kocer/direct-sampling-sdr/ardc/sema/dogrudan_sdr_D.pdf

File: 03_bias.kicad_sch Surucu katlari File: 01_driver.kicad_sch

Final kat File: 02_final.kicad_sch Guc ve koruma

File: 04_detect.kicad_sch Cikis filtreleri File: 05_lpf.kicad_sch Bias servosu

Donanim CERN-OHL-S-2.0 | HDL ve yazilim GPL-3.0-only | belgeler CC-BY-SA-4.0
Copyright (c) 2026 TA4DTA - lisans CERN-OHL-S-2.0
Baglantilar PA_TASARIM.md sartnamesinden
Lisans: CERN-OHL-S v2 (donanim) · GPL-3.0 (HDL) · CC-BY-SA 4.0 (dok)
TEVITOL amator telsiz kulubu / TA4DTA
Sheet: /
File: dogrudan_sdr_D.kicad_sch
Title: dogrudan_sdr_D — dogrudan orneklemeli HF/VHF/UHF transceiver

Size: A3 | Rev: A
KiCad E.D.A. 10.0.5 | Id: 1/7 | F Date:

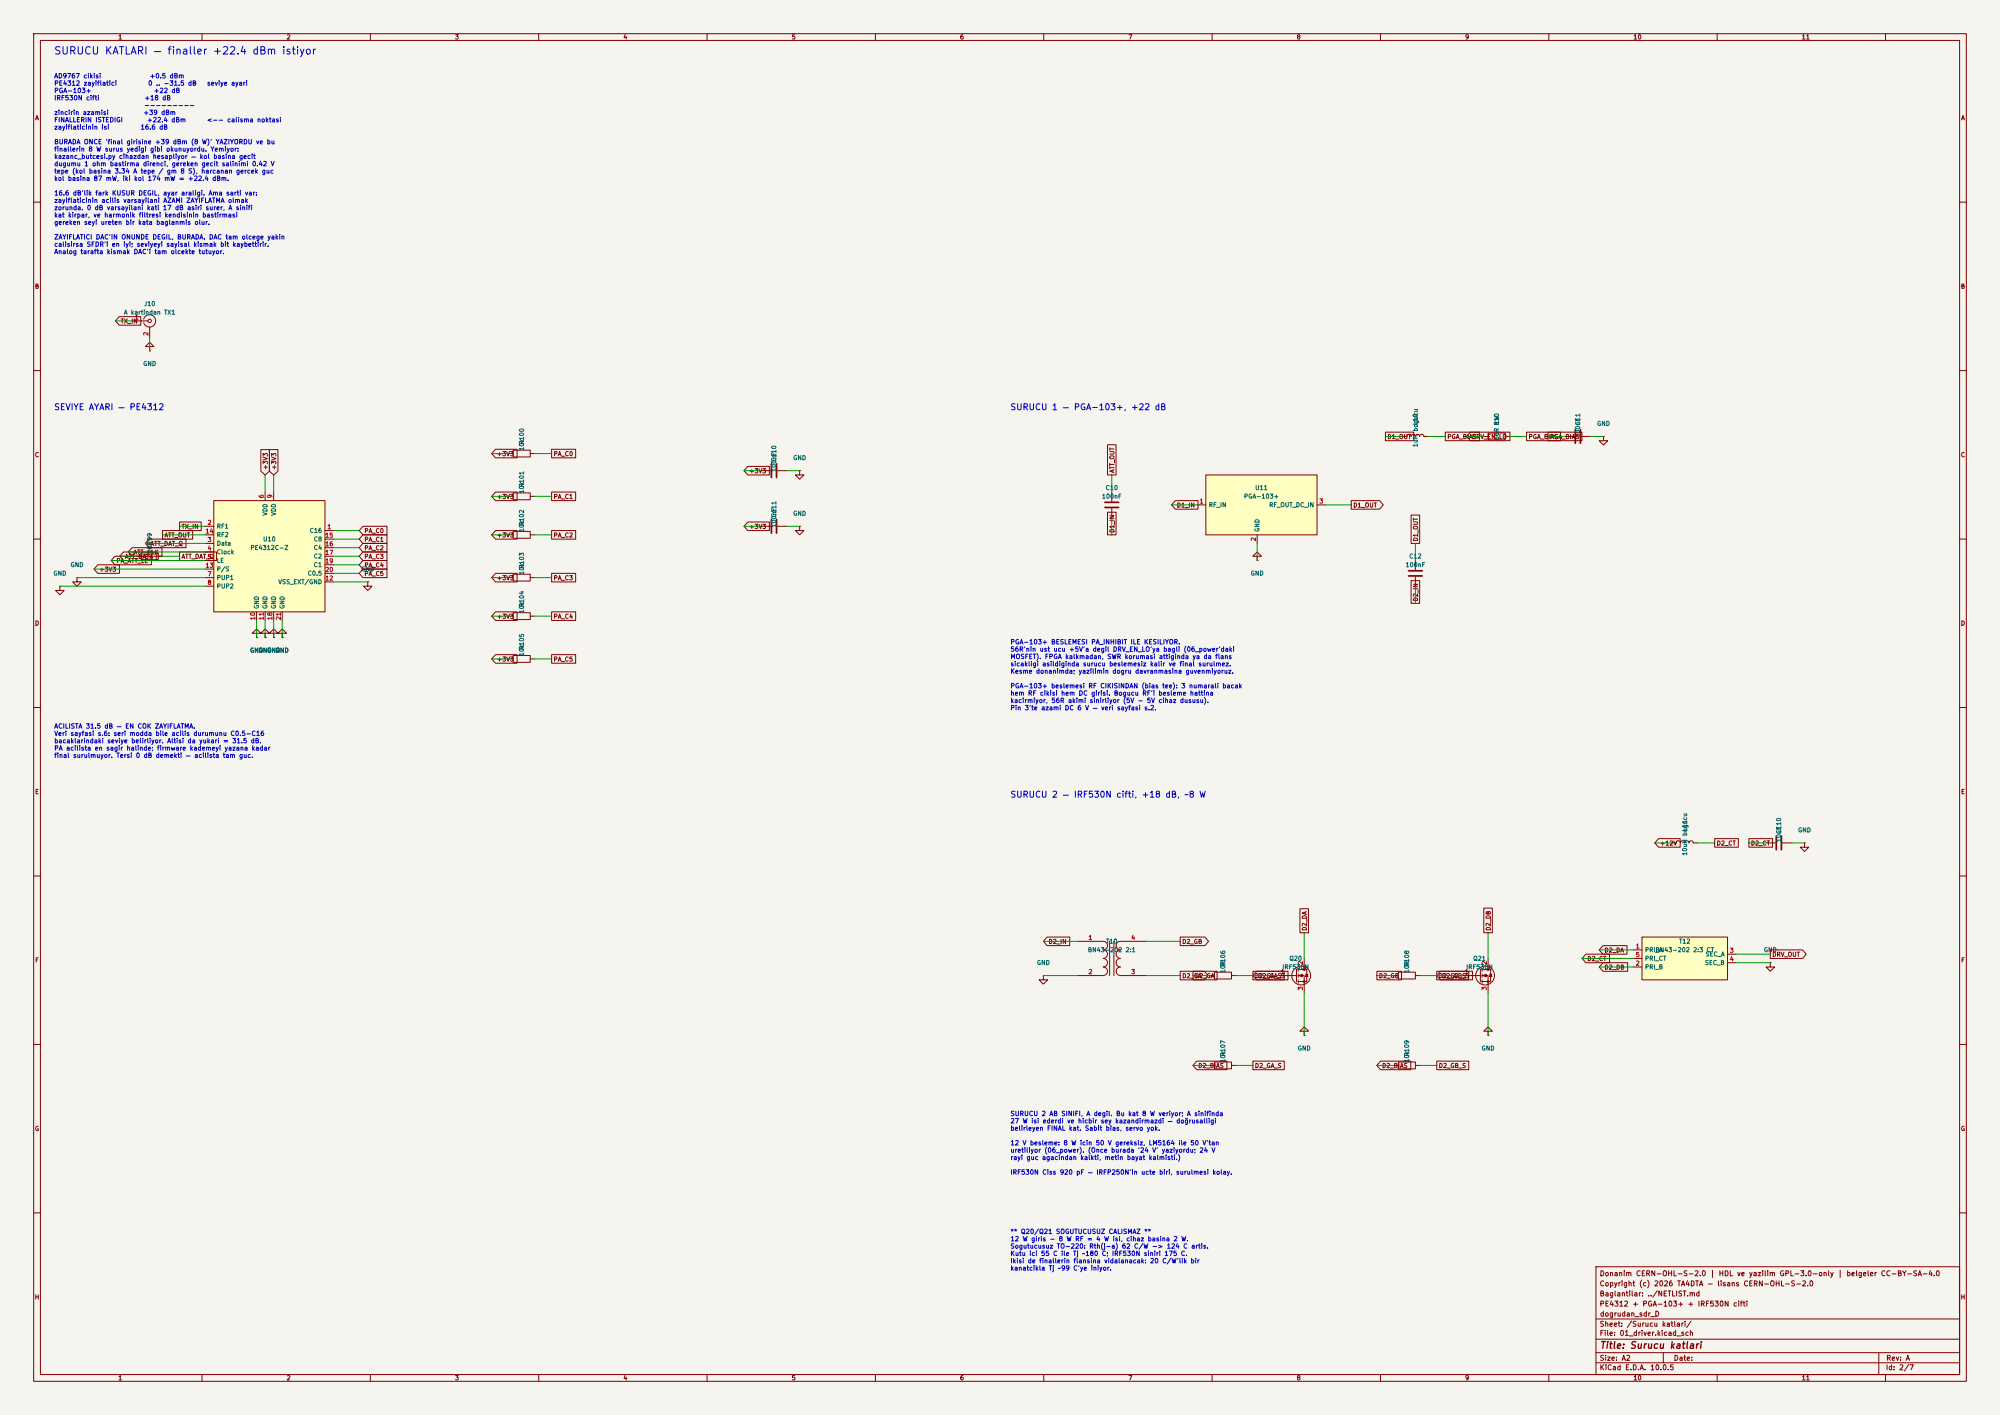
[picture p38: page 2]

SURUCU KATLARI — finaller +22.4 dBm istiyor

BURADA ONCE 'final girisine +39 dBm (8 W)' YAZIYORDU ve bu
finallerin 8 W surus yedigi gibi okunuyordu. Yemiyor:
kazanc_butcesi.py cihazdan hesapliyor — kol basina gecit
dugumu 1 ohm bastirma direnci, gereken gecit salinimi 0.42 V
tepe (kol basina 3.34 A tepe / gm 8 S), harcanan gercek guc
kol basina 87 mW, iki kol 174 mW = +22.4 dBm. 16.6 dB'lik fark KUSUR DEGIL, ayar araligi. Ama sarti var: zayiflaticinin acilis varsayilani AZAMI ZAYIFLATMA olmak

zorunda. 0 dB varsayilani kati 17 dB asiri surer, A sinifi kat kirpar, ve harmonik filtresi kendisinin bastirmasi gereken seyi ureten bir kata baglanmis olur. ZAYIFLATICI DAC'IN ONUNDE DEGIL, BURADA. DAC tam olcege yakin

calisirsa SFDR'i en iyi; seviyeyi sayisal kismak bit kaybettirir.
Analog tarafta kismak DAC'i tam olcekte tutuyor.

PGA-103+ BESLEMESI PA_INHIBIT ILE KESILIYOR. 56R'nin ust ucu +5V'a degil DRV_EN_LO'ya bagli (06_power'daki MOSFET). FPGA kalkmadan, SWR korumasi attiginda ya da flans

sicakligi asildiginda surucu beslemesiz kalir ve final surulmez. Kesme donanimda; yazilimin dogru davranmasina guvenmiyoruz. PGA-103+ beslemesi RF CIKISINDAN (bias tee): 3 numarali bacak hem RF cikisi hem DC girisi. Bogucu RF'i besleme hattina

kacirmiyor, 56R akimi sinirliyor (5V - 5V cihaz dususu). Pin 3'te azami DC 6 V — veri sayfasi s.2.

ACILISTA 31.5 dB — EN COK ZAYIFLATMA. Veri sayfasi s.6: seri modda bile acilis durumunu C0.5-C16

bacaklarindaki seviye belirliyor. Altisi da yukari = 31.5 dB. PA acilista en sagir halinde; firmware kademeyi yazana kadar

SURUCU 2 AB SINIFI, A degil. Bu kat 8 W veriyor; A sinifinda 27 W isi ederdi ve hicbir sey kazandirmazdi — doğrusalligi

belirleyen FINAL kat. Sabit bias, servo yok. 12 V besleme: 8 W icin 50 V gereksiz, LM5164 ile 50 V'tan

uretiliyor (06_power). (Once burada '24 V' yaziyordu; 24 V
rayi guc agacindan kalkti, metin bayat kalmisti.)

IRF530N Ciss 920 pF — IRFP250N'in ucte biri, surulmesi kolay. ** Q20/Q21 SOGUTUCUSUZ CALISMAZ ** 12 W giris - 8 W RF = 4 W isi, cihaz basina 2 W. Sogutucusuz TO-220: Rth(j-a) 62 C/W -> 124 C artis. Kutu ici 55 C ile Tj ~180 C; IRF530N siniri 175 C.

Ikisi de finallerin flansina vidalanacak: 20 C/W'lik bir kanatcikla Tj ~99 C'ye iniyor.

Donanim CERN-OHL-S-2.0 | HDL ve yazilim GPL-3.0-only | belgeler CC-BY-SA-4.0
Copyright (c) 2026 TA4DTA - lisans CERN-OHL-S-2.0
Baglantilar: ../NETLIST.md
PE4312 + PGA-103+ + IRF530N cifti
dogrudan_sdr_D
Sheet: /Surucu katlari/
File: 01_driver.kicad_sch
Title: Surucu katlari

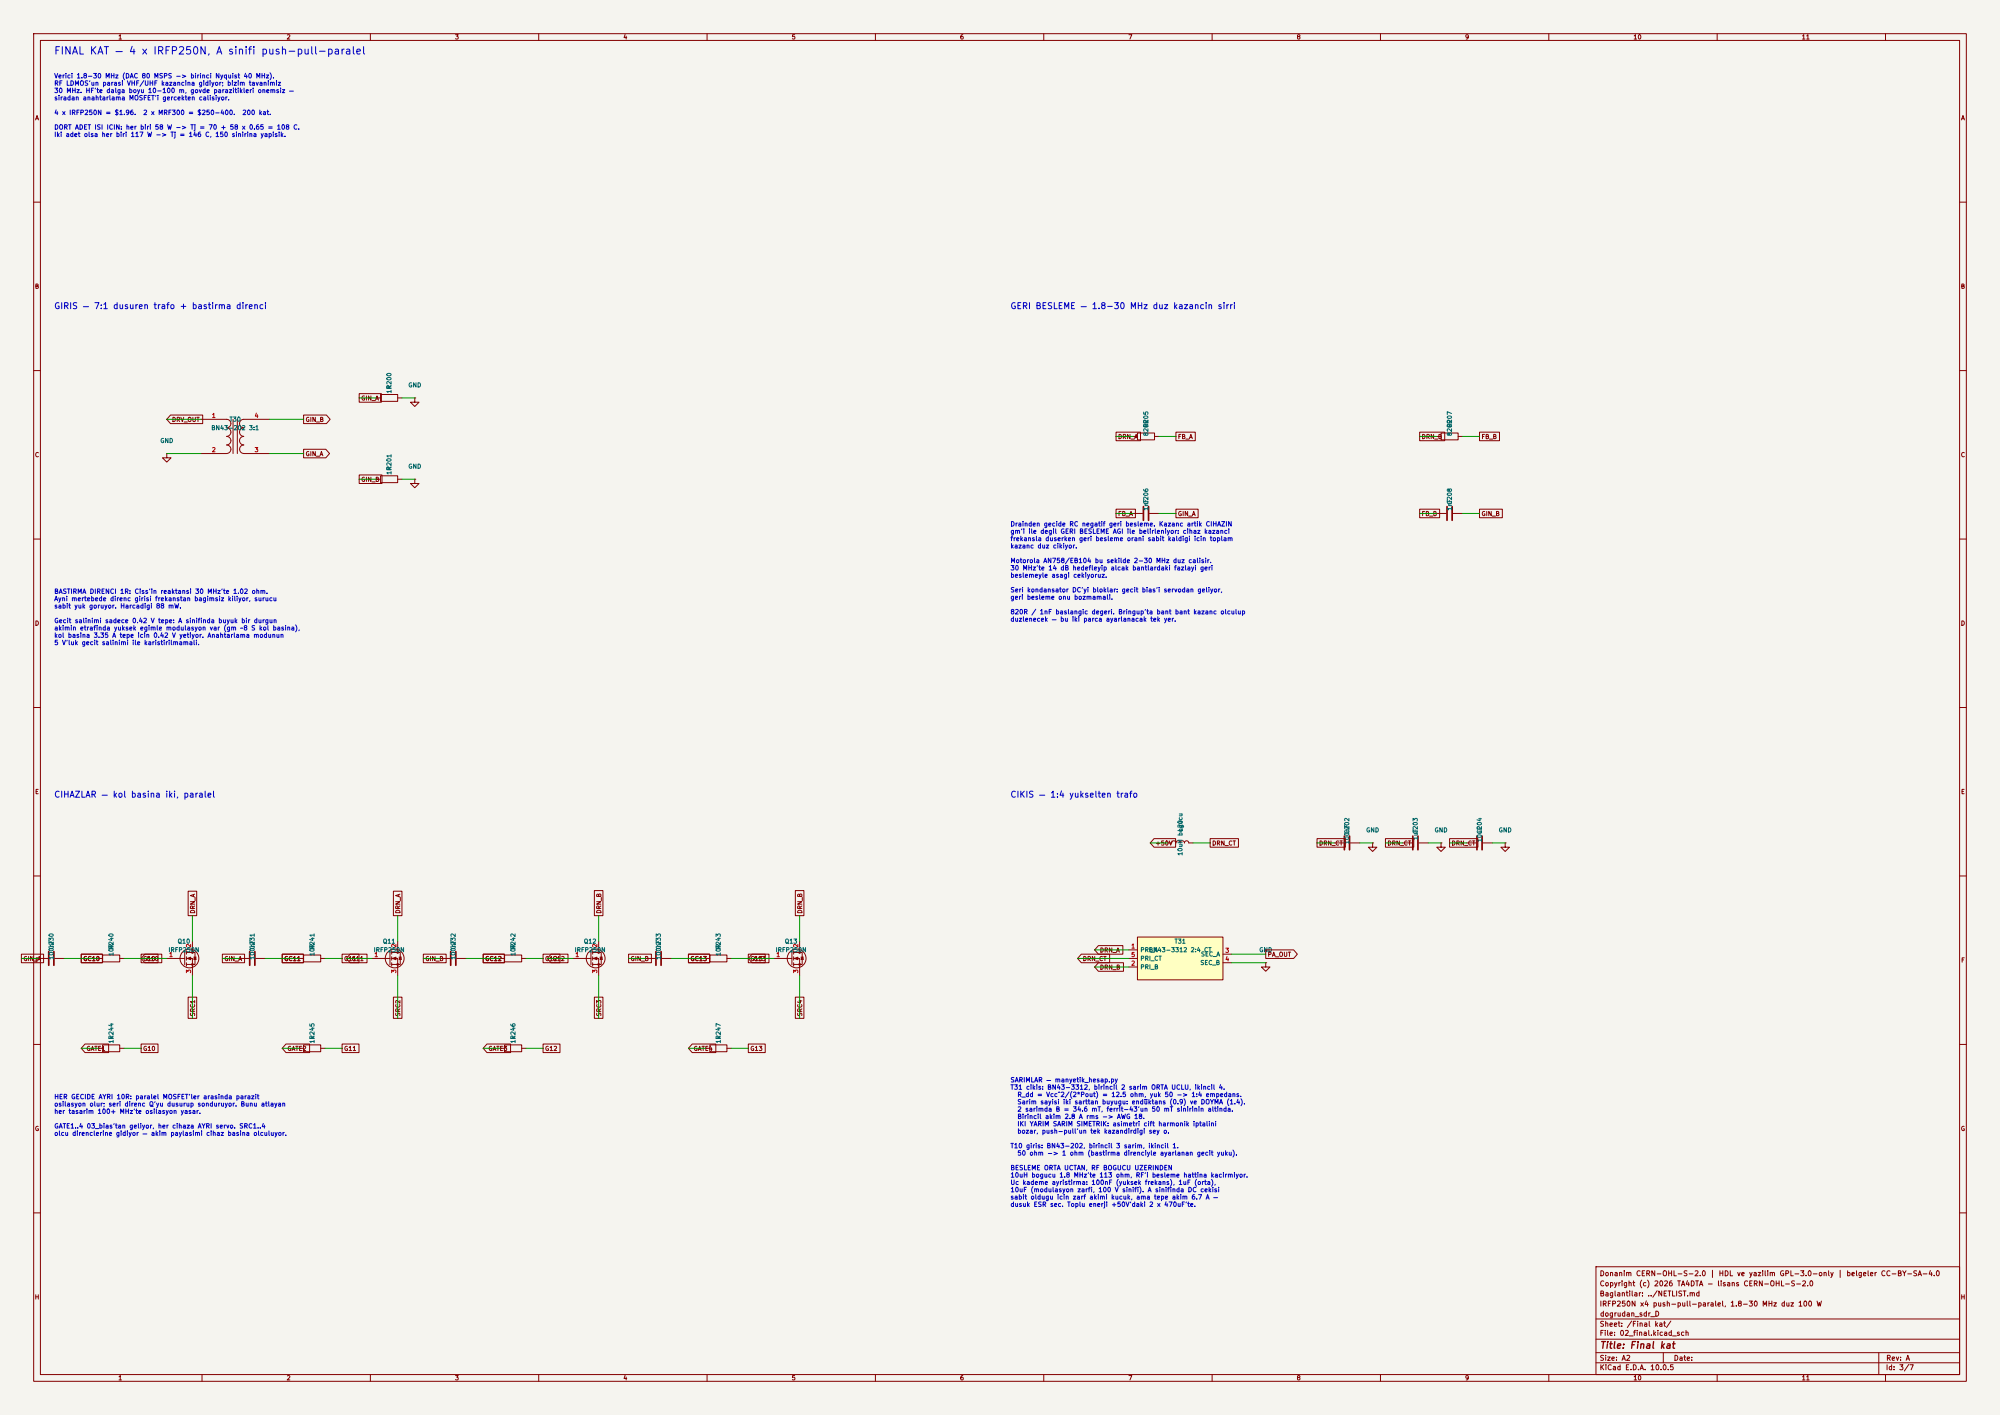
[picture p39: page 3]

FINAL KAT — 4 x IRFP250N, A sinifi push-pull-paralel

GIRIS — 7:1 dusuren trafo + bastirma direnci Verici 1.8-30 MHz (DAC 80 MSPS -> birinci Nyquist 40 MHz). RF LDMOS'un parasi VHF/UHF kazancina gidiyor; bizim tavanimiz 30 MHz. HF'te dalga boyu 10-100 m, govde parazitikleri onemsiz —

siradan anahtarlama MOSFET'i gercekten calisiyor. 4 x IRFP250N = $1.96. 2 x MRF300 = $250-400. 200 kat. DORT ADET ISI ICIN: her biri 58 W -> Tj = 70 + 58 x 0.65 = 108 C.

Iki adet olsa her biri 117 W -> Tj = 146 C, 150 sinirina yapisik.

GERI BESLEME — 1.8-30 MHz duz kazancin sirri BASTIRMA DIRENCI 1R: Ciss'in reaktansi 30 MHz'te 1.02 ohm. Ayni mertebede direnc girisi frekanstan bagimsiz kiliyor, surucu

gm'i ile degil GERI BESLEME AGI ile belirleniyor: cihaz kazanci frekansla duserken geri besleme orani sabit kaldigi icin toplam

kazanc duz cikiyor. Motorola AN758/EB104 bu sekilde 2-30 MHz duz calisir. 30 MHz'te 14 dB hedefleyip alcak bantlardaki fazlayi geri

beslemeyle asagi cekiyoruz. Seri kondansator DC'yi bloklar: gecit bias'i servodan geliyor,

sabit yuk goruyor. Harcadigi 88 mW. Gecit salinimi sadece 0.42 V tepe: A sinifinda buyuk bir durgun

geri besleme onu bozmamali. 820R / 1nF baslangic degeri. Bringup'ta bant bant kazanc olculup

akimin etrafinda yuksek egimle modulasyon var (gm ~8 S kol basina), kol basina 3.35 A tepe icin 0.42 V yetiyor. Anahtarlama modunun 5 V'luk gecit salinimi ile karistirilmamali.

duzlenecek — bu iki parca ayarlanacak tek yer. CIKIS — 1:4 yukselten trafo

T31 cikis: BN43-3312, birincil 2 sarim ORTA UCLU, ikincil 4. R_dd = Vcc^2/(2*Pout) = 12.5 ohm, yuk 50 -> 1:4 empedans. Sarim sayisi iki sarttan buyugu: endüktans (0.9) ve DOYMA (1.4). 2 sarimda B = 34.6 mT, ferrit-43'un 50 mT sinirinin altinda. Birincil akim 2.8 A rms -> AWG 18.

HER GECIDE AYRI 10R: paralel MOSFET'ler arasinda parazit
osilasyon olur; seri direnc Q'yu dusurup sonduruyor. Bunu atlayan
her tasarim 100+ MHz'te osilasyon yasar. GATE1..4 03_bias'tan geliyor, her cihaza AYRI servo. SRC1..4

IKI YARIM SARIM SIMETRIK: asimetri cift harmonik iptalini
bozar, push-pull'un tek kazandirdigi sey o. T10 giris: BN43-202, birincil 3 sarim, ikincil 1. 50 ohm -> 1 ohm (bastirma direnciyle ayarlanan gecit yuku). BESLEME ORTA UCTAN, RF BOGUCU UZERINDEN

olcu direnclerine gidiyor — akim paylasimi cihaz basina olculuyor.

10uH bogucu 1.8 MHz'te 113 ohm, RF'i besleme hattina kacirmiyor. Uc kademe ayristirma: 100nF (yuksek frekans), 1uF (orta), 10uF (modulasyon zarfi, 100 V sinifi). A sinifinda DC cekisi sabit oldugu icin zarf akimi kucuk, ama tepe akim 6.7 A —

Copyright (c) 2026 TA4DTA - lisans CERN-OHL-S-2.0

IRFP250N x4 push-pull-paralel, 1.8-30 MHz duz 100 W

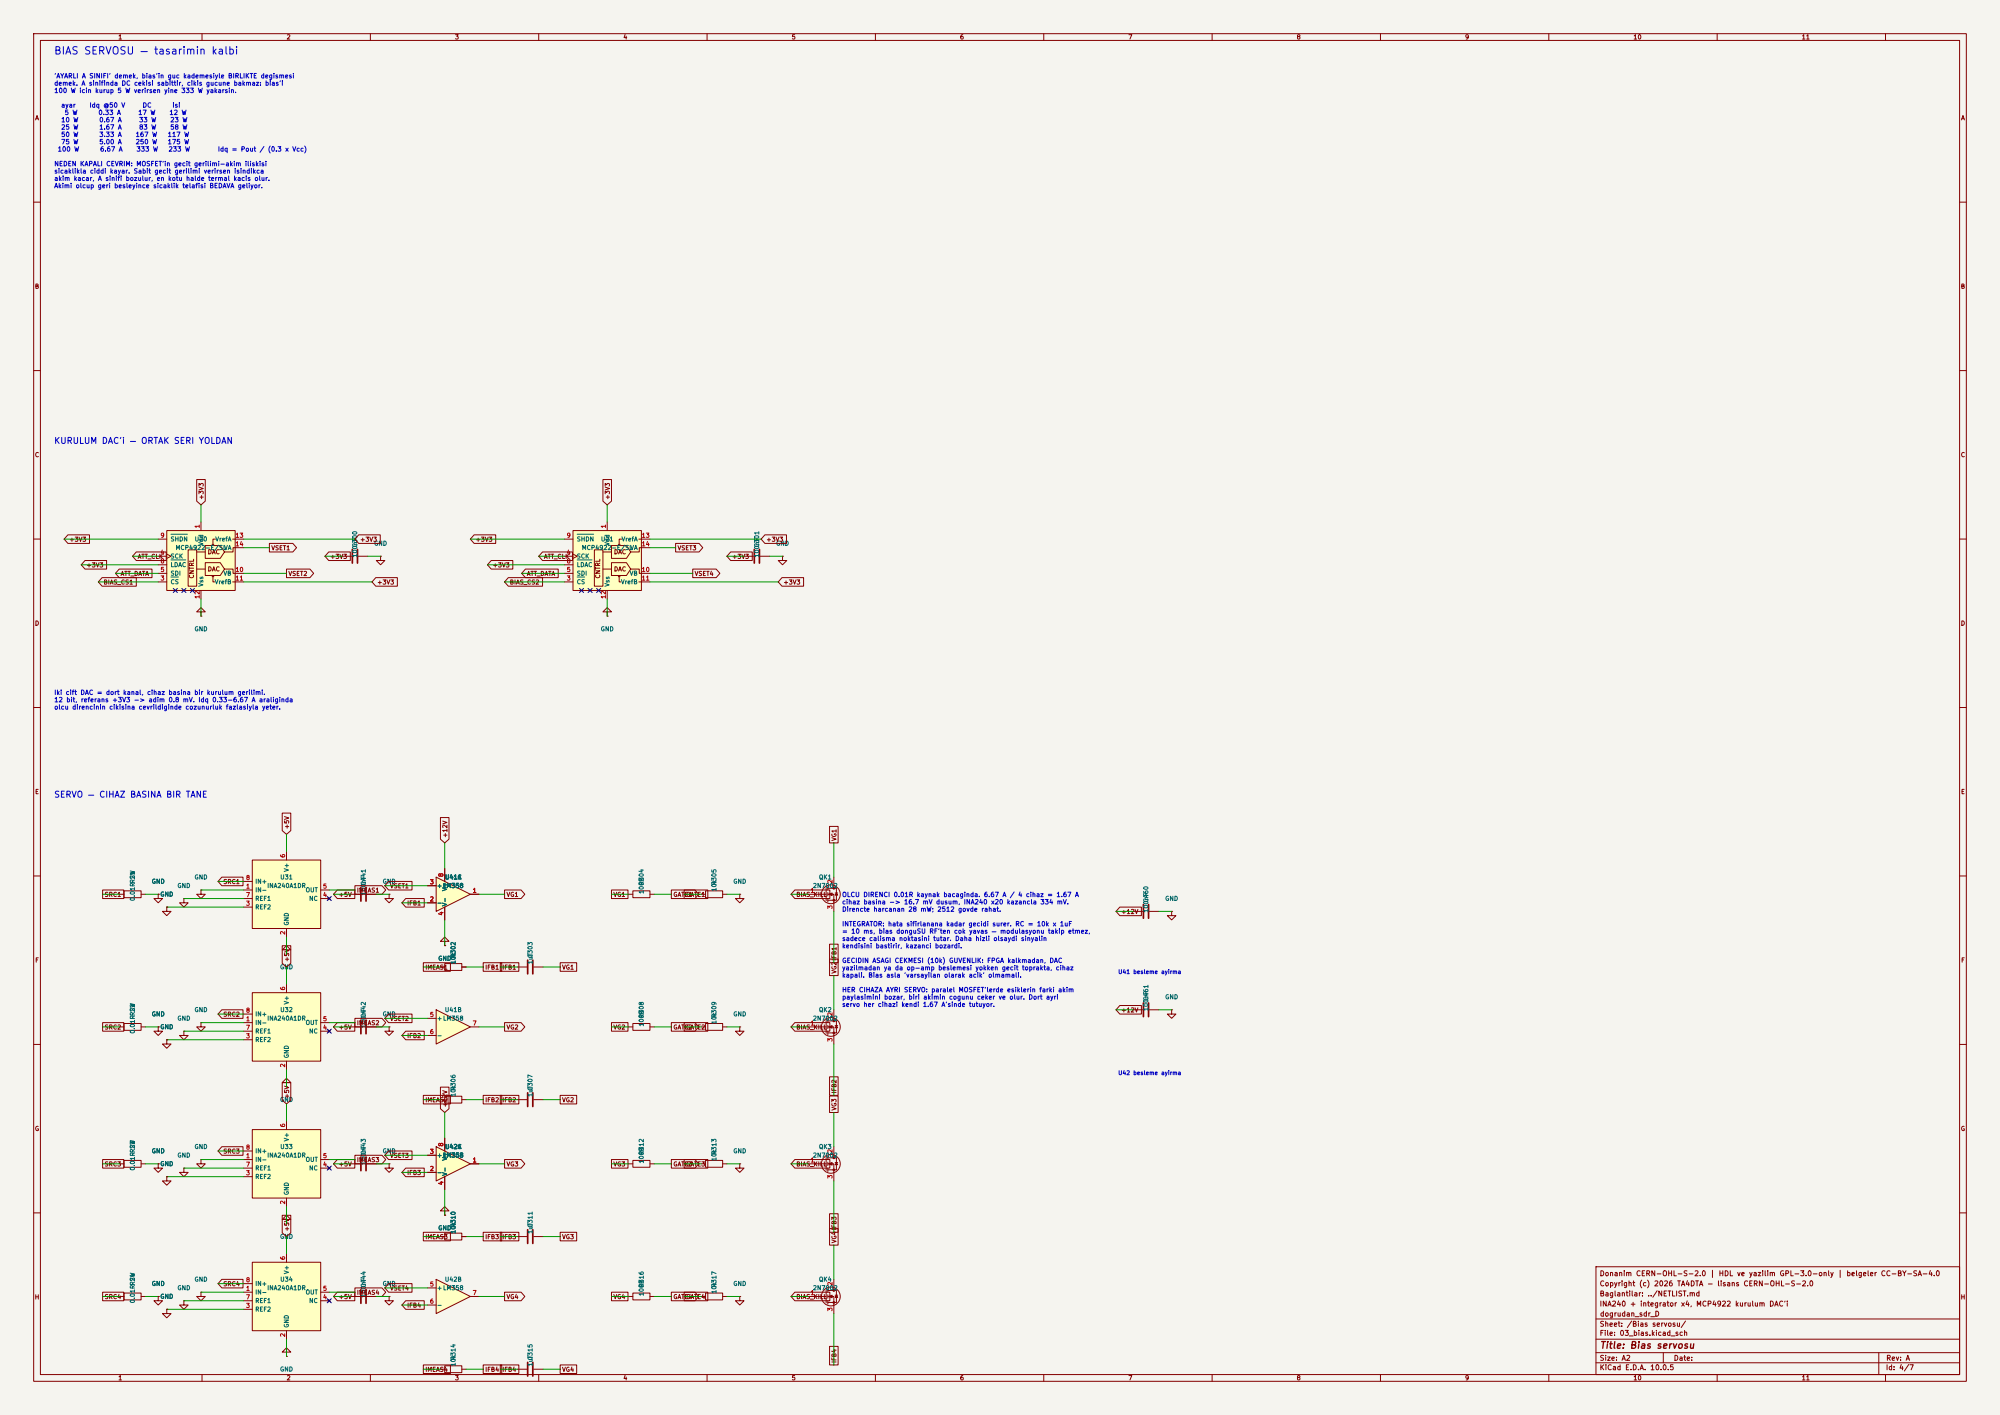
[picture p40: page 4]

BIAS SERVOSU — tasarimin kalbi

akim kacar, A sinifi bozulur, en kotu halde termal kacis olur. Akimi olcup geri besleyince sicaklik telafisi BEDAVA geliyor.

KURULUM DAC'i — ORTAK SERI YOLDAN

Iki cift DAC = dort kanal, cihaz basina bir kurulum gerilimi. 12 bit, referans +3V3 -> adim 0.8 mV. Idq 0.33-6.67 A araliginda

olcu direncinin cikisina cevrildiginde cozunurluk fazlasiyla yeter.

SERVO — CIHAZ BASINA BIR TANE

OLCU DIRENCI 0.01R kaynak bacaginda. 6.67 A / 4 cihaz = 1.67 A
cihaz basina -> 16.7 mV dusum, INA240 x20 kazancla 334 mV. Direncte harcanan 28 mW; 2512 govde rahat.

INTEGRATOR: hata sifirlanana kadar gecidi surer. RC = 10k x 1uF = 10 ms, bias donguSU RF'ten cok yavas — modulasyonu takip etmez, sadece calisma noktasini tutar. Daha hizli olsaydi sinyalin

kendisini bastirir, kazanci bozardi. GECIDIN ASAGI CEKMESI (10k) GUVENLIK: FPGA kalkmadan, DAC

yazilmadan ya da op-amp beslemesi yokken gecit toprakta, cihaz
kapali. Bias asla 'varsayilan olarak acik' olmamali. HER CIHAZA AYRI SERVO: paralel MOSFET'lerde esiklerin farki akim

Copyright (c) 2026 TA4DTA - lisans CERN-OHL-S-2.0

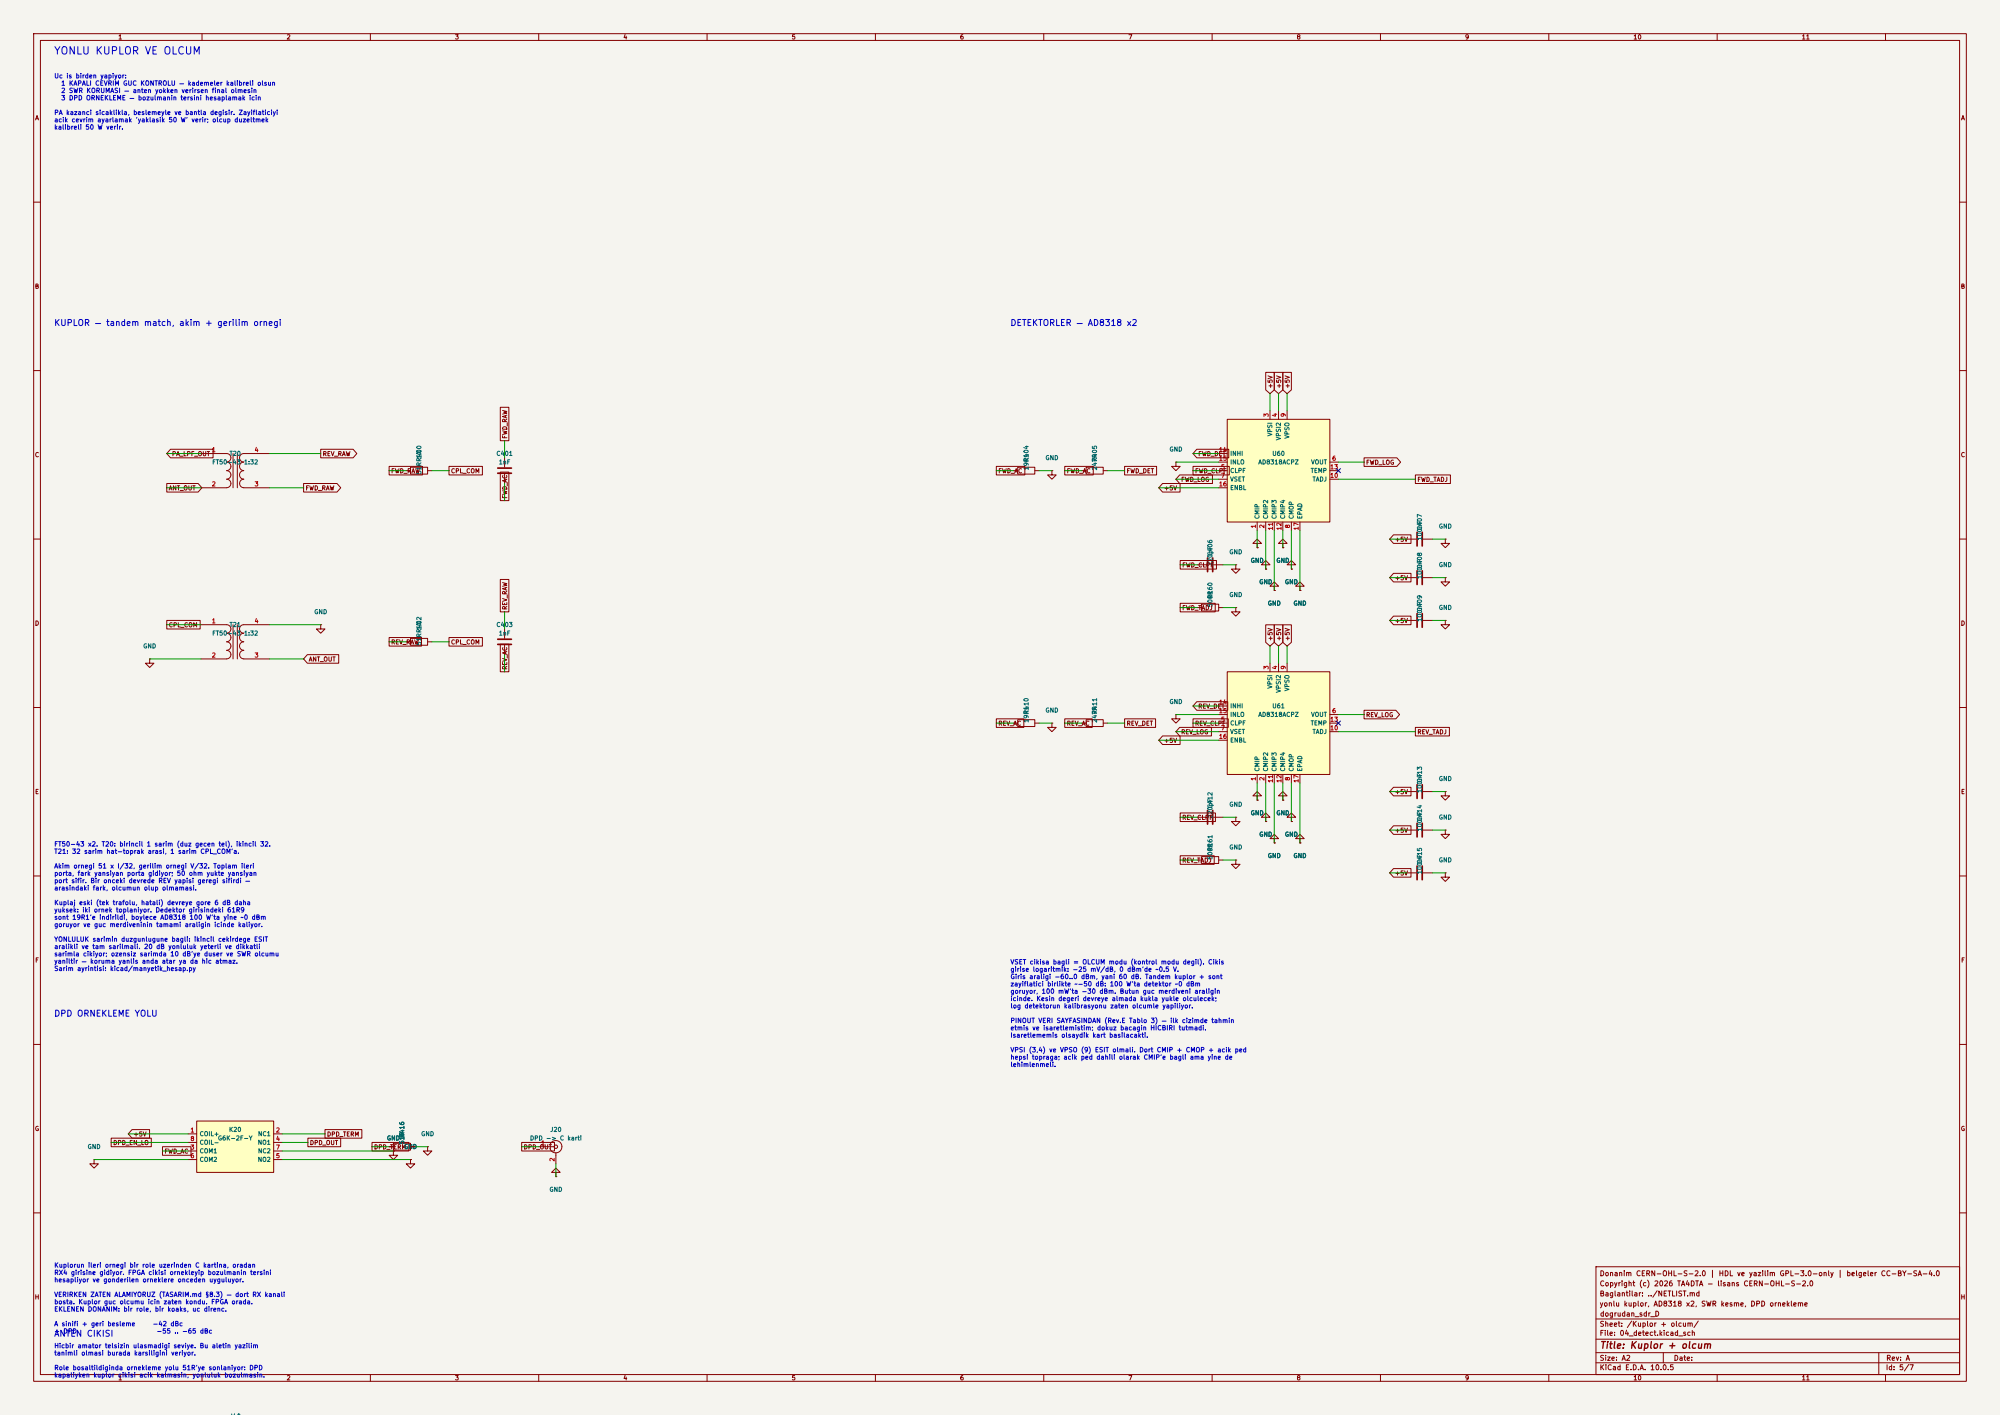
[picture p41: page 5]

YONLU KUPLOR VE OLCUM

Uc is birden yapiyor: 1 KAPALI CEVRIM GUC KONTROLU — kademeler kalibreli olsun 2 SWR KORUMASI — anten yokken verirsen final olmesin 3 DPD ORNEKLEME — bozulmanin tersini hesaplamak icin PA kazanci sicaklikla, beslemeyle ve bantla degisir. Zayiflaticiyi acik cevrim ayarlamak 'yaklasik 50 W' verir; olcup duzeltmek

KUPLOR — tandem match, akim + gerilim ornegi

FT50-43 x2. T20: birincil 1 sarim (duz gecen tel), ikincil 32. T21: 32 sarim hat-toprak arasi, 1 sarim CPL_COM'a. Akim ornegi 51 x I/32, gerilim ornegi V/32. Toplam ileri porta, fark yansiyan porta gidiyor; 50 ohm yukte yansiyan

port sifir. Bir onceki devrede REV yapisi geregi sifirdi —
arasindaki fark, olcumun olup olmamasi. Kuplaj eski (tek trafolu, hatali) devreye gore 6 dB daha

yuksek: iki ornek toplaniyor. Dedektor girisindeki 61R9
sont 19R1'e indirildi, boylece AD8318 100 W'ta yine ~0 dBm
goruyor ve guc merdiveninin tamami araligin icinde kaliyor. YONLULUK sarimin duzgunlugune bagli: ikincil cekirdege ESIT aralikli ve tam sarilmali. 20 dB yonluluk yeterli ve dikkatli sarimla cikiyor; ozensiz sarimda 10 dB'ye duser ve SWR olcumu

FGH
yaniltir — koruma yanlis anda atar ya da hic atmaz. Sarim ayrintisi: kicad/manyetik_hesap.py

VSET cikisa bagli = OLCUM modu (kontrol modu degil). Cikis girise logaritmik: -25 mV/dB, 0 dBm'de ~0.5 V. Giris araligi -60..0 dBm, yani 60 dB. Tandem kuplor + sont zayiflatici birlikte ~-50 dB: 100 W'ta detektor ~0 dBm

goruyor, 100 mW'ta -30 dBm. Butun guc merdiveni araligin
icinde. Kesin degeri devreye almada kukla yukle olculecek;
log detektorun kalibrasyonu zaten olcumle yapiliyor. PINOUT VERI SAYFASINDAN (Rev.E Tablo 3) — ilk cizimde tahmin

etmis ve isaretlemistim; dokuz bacagin HICBIRI tutmadi.
Isaretlememis olsaydik kart basilacakti. VPSI (3,4) ve VPSO (9) ESIT olmali. Dort CMIP + CMOP + acik ped

hepsi topraga; acik ped dahili olarak CMIP'e bagli ama yine de

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

yonlu kuplor, AD8318 x2, SWR kesme, DPD ornekleme

tanimli olmasi burada karsiligini veriyor. Role bosaltildiginda ornekleme yolu 51R'ye sonlaniyor: DPD

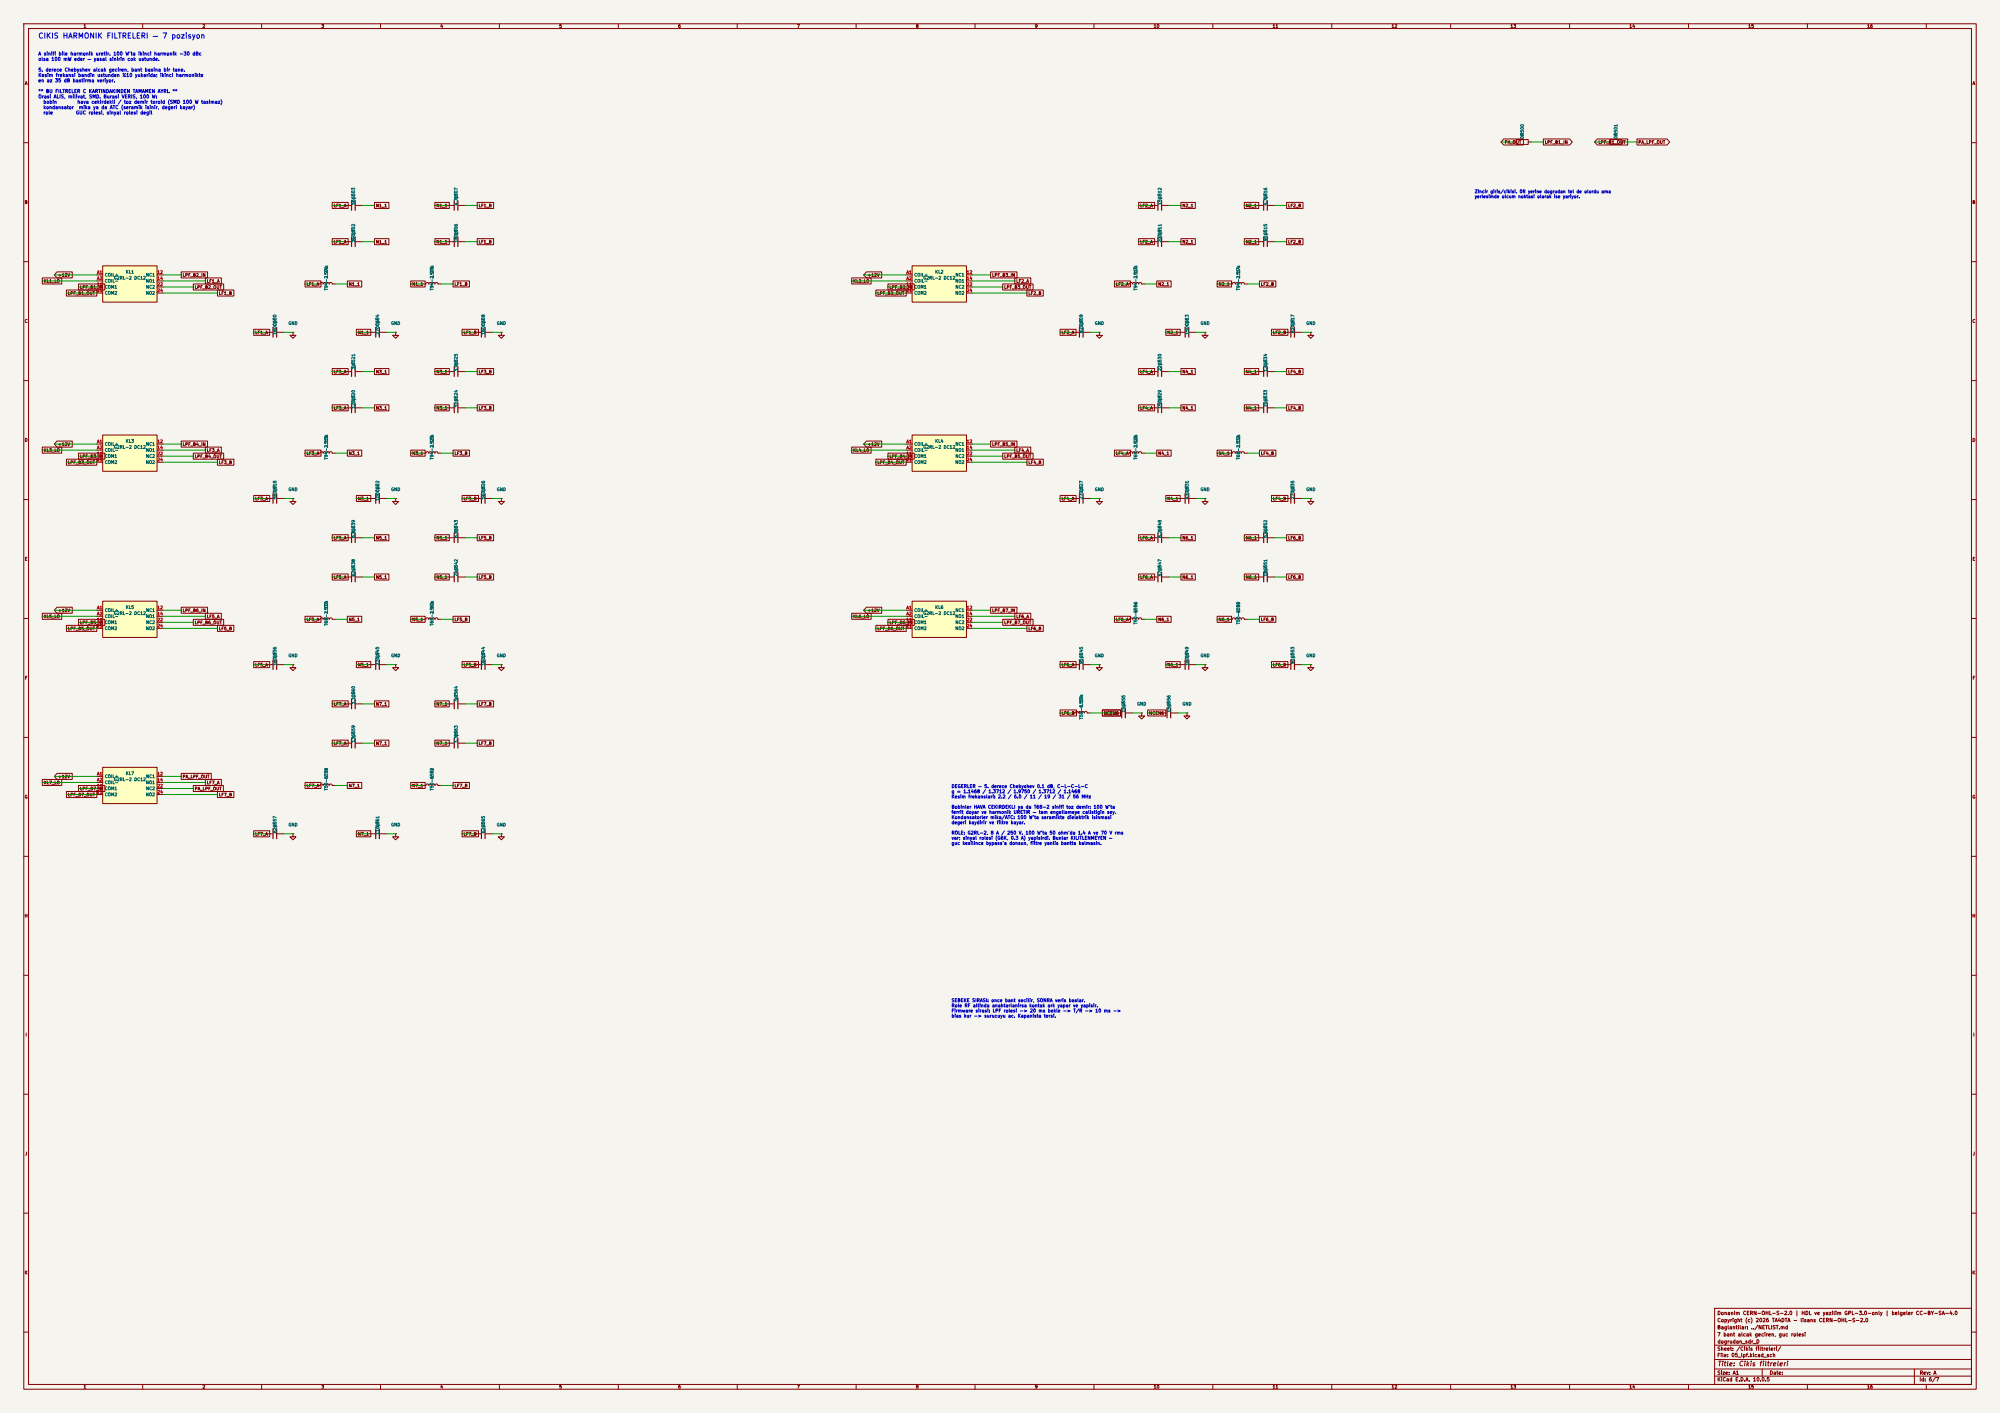
[picture p42: page 6]

CIKIS HARMONIK FILTRELERI — 7 pozisyon

A sinifi bile harmonik uretir. 100 W'ta ikinci harmonik -30 dBc olsa 100 mW eder — yasal sinirin cok ustunde. 5. derece Chebyshev alcak geciren, bant basina bir tane. Kesim frekansi bandin ustunden %10 yukarida; ikinci harmonikte

yerlesimde olcum noktasi olarak ise yariyor.

DEGERLER — 5. derece Chebyshev 0.1 dB, C-L-C-L-C
g = 1.1468 / 1.3712 / 1.9750 / 1.3712 / 1.1468 Kesim frekanslari: 2.2 / 6.0 / 11 / 19 / 31 / 56 MHz Bobinler HAVA CEKIRDEKLI ya da T68-2 sinifi toz demir: 100 W'ta

ferrit doyar ve harmonik URETIR — tam engellemeye calistigin sey. Kondansatorler mika/ATC: 100 W'ta seramikte dielektrik isinmasi degeri kaydirir ve filtre kayar. ROLE: G2RL-2, 8 A / 250 V. 100 W'ta 50 ohm'da 1.4 A ve 70 V rms

var; sinyal rolesi (G6K, 0.3 A) yapisirdi. Bunlar KILITLENMEYEN —
guc kesilince bypass'a donsun, filtre yanlis bantta kalmasin.

SEBEKE SIRASI: once bant secilir, SONRA veris baslar. Role RF altinda anahtarlanirsa kontak ark yapar ve yapisir. Firmware sirasi: LPF rolesi -> 20 ms bekle -> T/R -> 10 ms ->

bias kur -> surucuyu ac. Kapanista tersi.

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

7 bant alcak geciren, guc rolesi

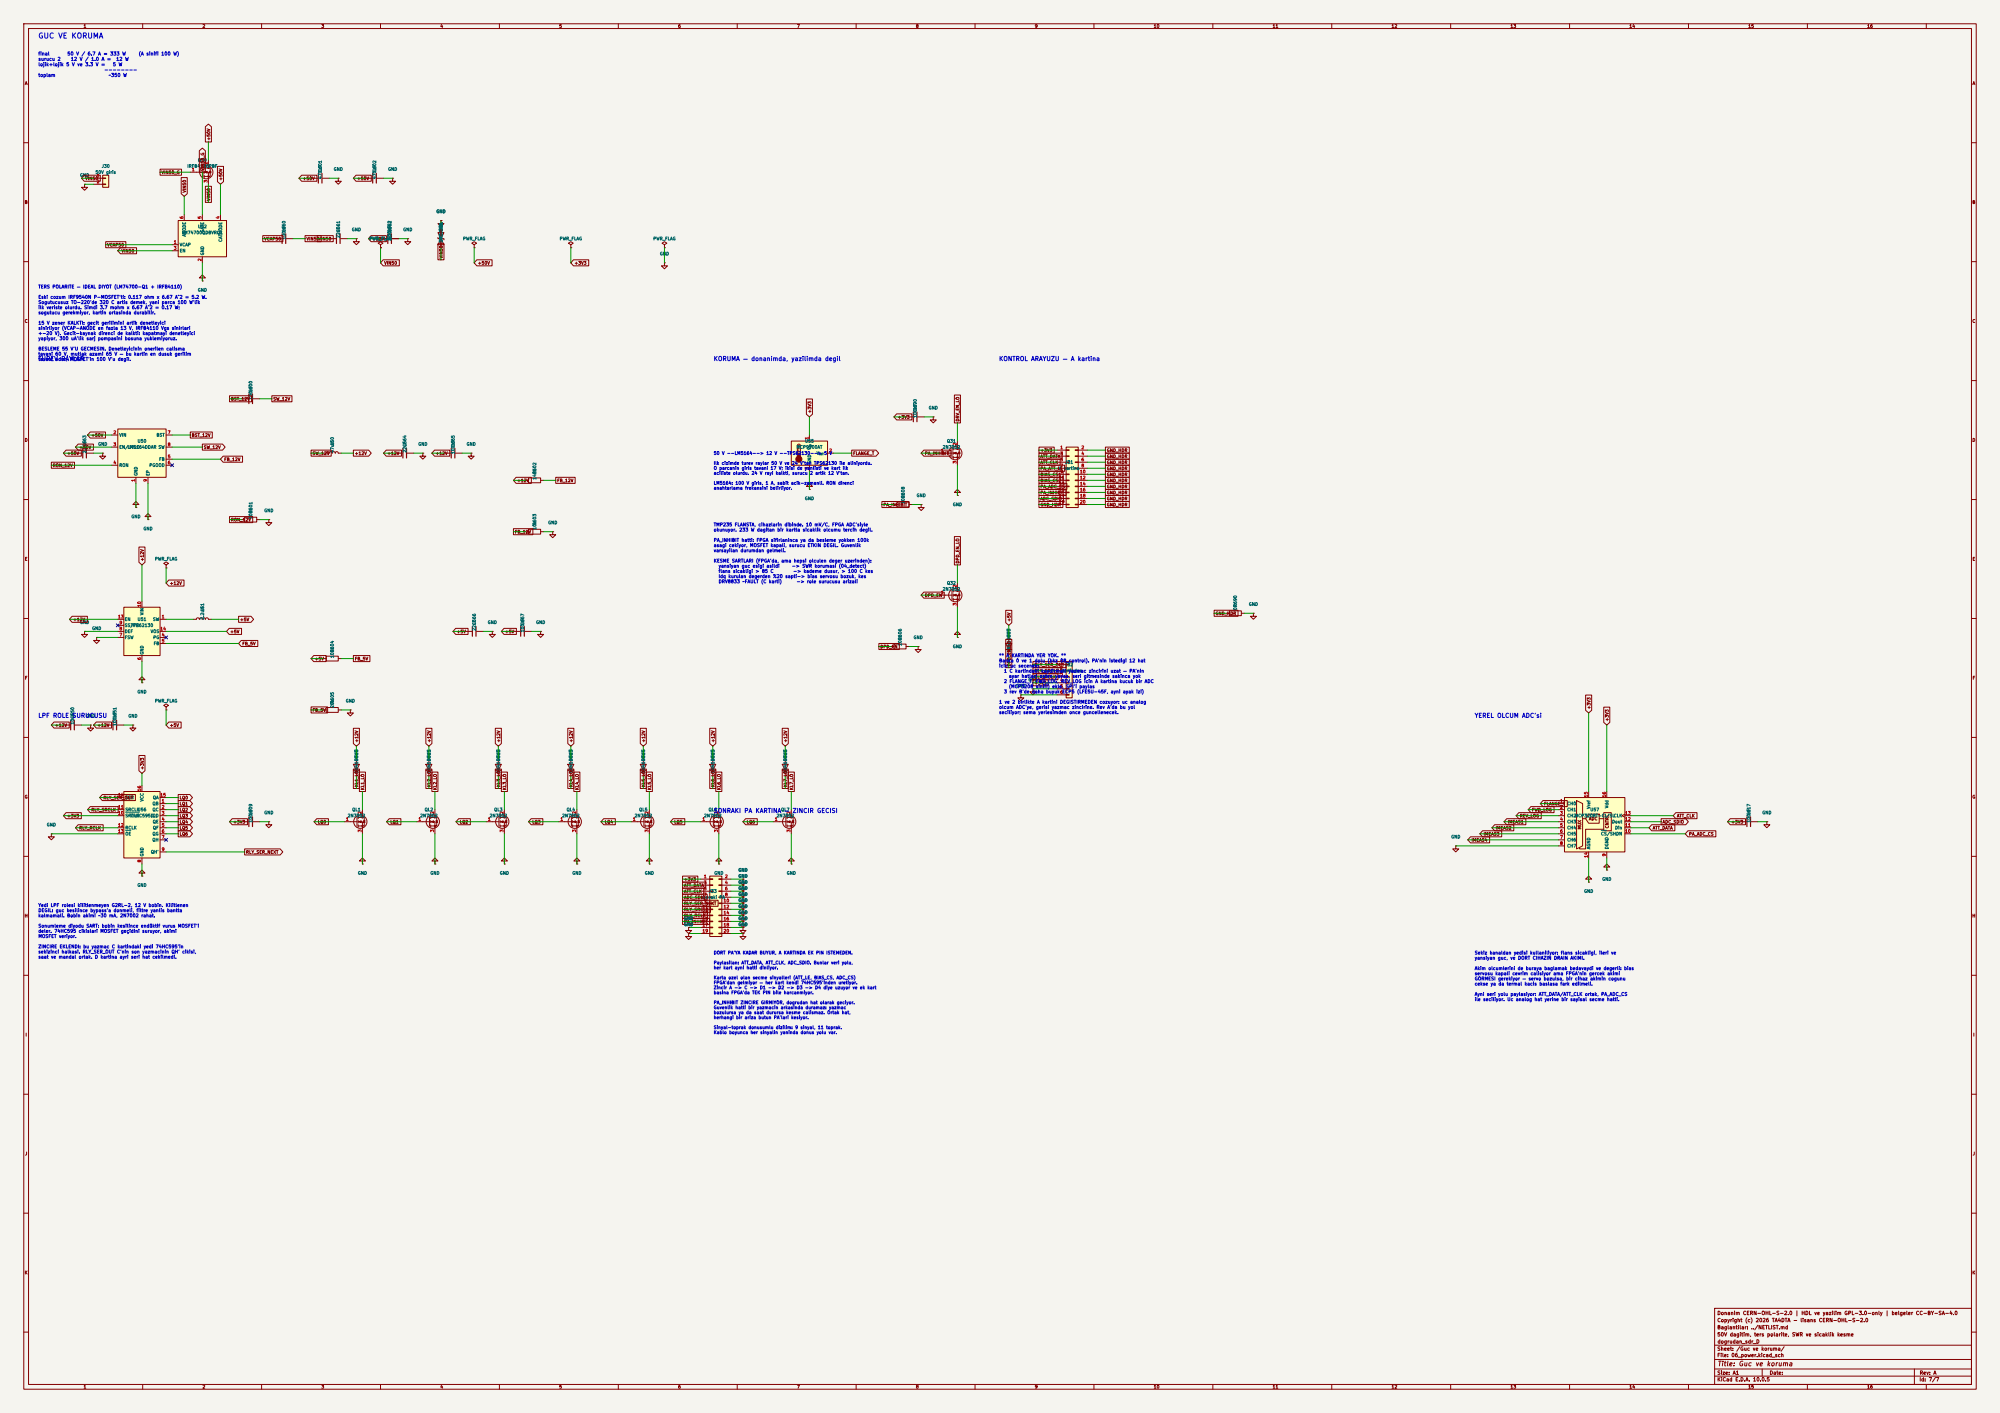
[picture p43: page 7]

TERS POLARITE — IDEAL DIYOT (LM74700-Q1 + IRFB4110) Eski cozum IRF9540N P-MOSFET'ti: 0.117 ohm x 6.67 A^2 = 5.2 W. Sogutucusuz TO-220'de 320 C artis demek, yani parca 100 W'lik

ilk veriste olurdu. Simdi 3.7 mohm x 6.67 A^2 = 0.17 W;
sogutucu gerekmiyor, kartin ortasinda durabilir. 15 V zener KALKTI: gecit gerilimini artik denetleyici
sinirliyor (VCAP-ANODE en fazla 13 V, IRFB4110 Vgs sinirlari +-20 V). Gecit-kaynak direnci de kalkti: kapatmayi denetleyici

yapiyor, 300 uA'lik sarj pompasini bosuna yuklemiyoruz. BESLEME 55 V'U GECMESIN. Denetleyicinin onerilen calisma

tavani 60 V, mutlak azami 65 V — bu kartin en dusuk gerilim TUREV tavani odur, RAYLAR MOSFET'in 100 V'u degil.

KORUMA — donanimda, yazilimda degil

TMP235 FLANSTA, cihazlarin dibinde. 10 mV/C, FPGA ADC'siyle
okunuyor. 233 W dagitan bir kartta sicaklik olcumu tercih degil.

PA_INHIBIT hatti: FPGA sifirlaninca ya da besleme yokken 100k asagi cekiyor, MOSFET kapali, surucu ETKIN DEGIL. Guvenlik

varsayilan durumdan gelmeli. KESME SARTLARI (FPGA'da, ama hepsi olculen deger uzerinden):

olcum ADC'ye, gerisi yazmac zincirine. Rev A'da bu yol
seciliyor; sema yerlesimden once guncellenecek.

YEREL OLCUM ADC'si

SRCLR 10 SRCLK 11 RCLK 12 OE 13

Yedi LPF rolesi kilitlenmeyen G2RL-2, 12 V bobin. Kilitlenen DEGIL: guc kesilince bypass'a donmeli, filtre yanlis bantta

kalmamali. Bobin akimi ~30 mA, 2N7002 rahat. Sonumleme diyodu SART: bobin kesilince endüktif vurus MOSFET'i deler. 74HC595 cikislari MOSFET geçidini suruyor, akimi MOSFET veriyor. ZINCIRE EKLENDI: bu yazmac C kartindaki yedi 74HC595'in

sekizinci halkasi. RLY_SER_OUT C'nin son yazmacinin QH' cikisi, saat ve mandal ortak. D kartina ayri seri hat cekilmedi.

DORT PA'YA KADAR BUYUR, A KARTINDA EK PIN ISTEMEDEN. Paylasilan: ATT_DATA, ATT_CLK, ADC_SDIO. Bunlar veri yolu, her kart ayni hatti dinliyor. Karta ozel olan secme sinyalleri (ATT_LE, BIAS_CS, ADC_CS) FPGA'dan gelmiyor — her kart kendi 74HC595'inden uretiyor. Zincir A -> C -> D1 -> D2 -> D3 -> D4 diye uzuyor ve ek kart basina FPGA'da TEK PIN bile harcanmiyor. PA_INHIBIT ZINCIRE GIRMIYOR, dogrudan hat olarak geciyor. Guvenlik hatti bir yazmacin arkasinda duramaz: yazmac bozulursa ya da saat durursa kesme calismaz. Ortak hat,

Sekiz kanaldan yedisi kullaniliyor: flans sicakligi, ileri ve
yansiyan guc, ve DORT CIHAZIN DRAIN AKIMI. Akim olcumlerini de buraya baglamak bedavaydi ve degerli: bias

servosu kapali cevrim calisiyor ama FPGA'nin gercek akimi GORMESI gerekiyor — servo bozulsa, bir cihaz akimin cogunu

cekse ya da termal kacis baslasa fark edilmeli. Ayni seri yolu paylasiyor: ATT_DATA/ATT_CLK ortak, PA_ADC_CS

ile seciliyor. Uc analog hat yerine bir sayisal secme hatti.

herhangi bir ariza butun PA'lari kesiyor.

Sinyal-toprak donusumlu dizilim: 9 sinyal, 11 toprak. Kablo boyunca her sinyalin yaninda donus yolu var.

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

50V dagitim, ters polarite, SWR ve sicaklik kesme

Sheet: /Guc ve koruma/
File: 06_power.kicad_sch
Title: Guc ve koruma
